sherry144260/hitcon-pcb-badge/fw/Core/Hitcon/App/tama_src/screens.h

#ifndef SCREENS_H
#define SCREENS_H

#include "simu_setting.h"
/// -- -- -- --

#define DISPLAY_WIDTH 16
#define DISPLAY_HEIGHT 8
#define COMMON_HEIGHT 8
#define IDLE_PET_WIDTH 8
#define SELECT_WIDTH 8
#define NUM_WIDTH 2
#define EGG_WIDTH 8
#define FOOD_HEART_OVERVIEW_ICON_WIDTH 4
#define FOOD_HEART_OVERVIEW_ICON_HEIGHT 4
#define WEAK_PET_WIDTH 8
#define WEAK_PET_PARTICLE_WIDTH 8
#define HOSPITAL_WIDTH 8
#define BATTLE_WIDTH 7
#define TRAINING_WIDTH 7
#define YN_WIDTH 16
#define YN_SELECT_LEFT_WIDTH 4
#define YN_SELECT_RIGHT_WIDTH 3

// m_xxx = material xxx

enum {
  FRAME_1,
  FRAME_2,
};

enum {
  PET_TYPE_DOG,
  PET_TYPE_CAT,
  OTHER_TYPE_TRAINING_FACILITY,
};

enum {
  BATTLE,
  TRAINING,
};

enum {
  LEFT,
  RIGHT,
};

enum {
  WIN,
  LOSE,
};

enum {
  PLAYER,
  ENEMY,
  NONE,
};

enum {
  cookie_100,
  cookie_50,
  cookie_30,
  cookie_0,
  ate_frame0,
  ate_frame1,
};

// the structure of compressed data
struct CompressedImage {
  uint8_t width;        // image width info
  uint8_t height;       // image height info
  const uint8_t* data;  // the pointer to the data
};

namespace hitcon {
namespace app {
namespace tama {
namespace components {

/**
 * @brief The compressed data of dog idle1.
 *
 * The original data is:
 *
 *  ```
 *  0, 0, 0, 0, 0, 0, 0, 0,  //
 *  0, 0, 0, 0, 0, 0, 0, 0,  //
 *  0, 0, 0, 0, 1, 0, 1, 0,  //
 *  1, 0, 0, 1, 1, 1, 1, 0,  //
 *  1, 0, 1, 1, 1, 1, 1, 1,  //
 *  1, 1, 1, 1, 1, 1, 1, 0,  //
 *  0, 1, 1, 1, 1, 1, 1, 0,  //
 *  0, 1, 0, 1, 0, 1, 0, 0,  //
 *  ```
 *
 * Notice: the compressed data is not directly mapping to the original data.
 * It packed the bits in a specific way.
 *
 */
constexpr uint8_t m_dog_idle1_compressed_data[] = {0x38, 0xE0, 0x70, 0xF8,
                                                   0x7C, 0xF8, 0x7C, 0x10};
constexpr CompressedImage m_dog_idle1_compressed = {
    .width = IDLE_PET_WIDTH,
    .height = COMMON_HEIGHT,
    .data = m_dog_idle1_compressed_data};

/**
 * @brief The compressed data of dog idle2.
 *
 * The original data is:
 *
 *  ```
 *  0, 0, 0, 0, 0, 0, 0, 0,  //
 *  0, 0, 0, 0, 0, 0, 0, 0,  //
 *  0, 0, 0, 0, 1, 0, 1, 0,  //
 *  0, 0, 0, 1, 1, 1, 1, 0,  //
 *  1, 0, 1, 1, 1, 1, 1, 1,  //
 *  1, 1, 1, 1, 1, 1, 1, 0,  //
 *  0, 1, 1, 1, 1, 1, 1, 0,  //
 *  0, 1, 0, 1, 0, 1, 0, 0,  //
 *  ```
 *
 * Notice: the compressed data is not directly mapping to the original data.
 * It packed the bits in a specific way.
 *
 */
constexpr uint8_t m_dog_idle2_compressed_data[] = {0x30, 0xE0, 0x70, 0xF8,
                                                   0x7C, 0xF8, 0x7C, 0x10};
constexpr CompressedImage m_dog_idle2_compressed = {
    .width = IDLE_PET_WIDTH,
    .height = COMMON_HEIGHT,
    .data = m_dog_idle2_compressed_data};

/**
 * @brief The compressed data of m_cat_idle1.
 *
 * The original data is:
 *
 *  ```
    0, 0, 0, 0, 0, 0, 0, 0,  //
    0, 0, 0, 0, 0, 0, 0, 0,  //
    0, 0, 0, 0, 0, 0, 0, 0,  //
    0, 0, 1, 0, 1, 0, 1, 0,  //
    0, 1, 0, 0, 1, 1, 1, 0,  //
    0, 1, 0, 1, 1, 1, 1, 0,  //
    0, 0, 1, 1, 1, 1, 1, 0,  //
    0, 0, 1, 0, 1, 0, 1, 0,  //
 *  ```
 *
 * Notice: the compressed data is not directly mapping to the original data.
 * It packed the bits in a specific way.
 *
 */
constexpr uint8_t m_cat_idle1_compressed_data[] = {0x00, 0x30, 0xC8, 0x60,
                                                   0xF8, 0x70, 0xF8, 0x00};
constexpr CompressedImage m_cat_idle1_compressed = {
    .width = IDLE_PET_WIDTH,
    .height = COMMON_HEIGHT,
    .data = m_cat_idle1_compressed_data};

/**
 * @brief The compressed data of m_cat_idle2.
 *
 * The original data is:
 *
 *  ```
 *  0, 0, 0, 0, 0, 0, 0, 0,  //
 *  0, 0, 0, 0, 0, 0, 0, 0,  //
 *  0, 0, 0, 0, 0, 0, 0, 0,  //
 *  1, 1, 0, 0, 1, 0, 1, 0,  //
 *  0, 0, 1, 0, 1, 1, 1, 0,  //
 *  0, 1, 0, 1, 1, 1, 1, 0,  //
 *  0, 0, 1, 1, 1, 1, 1, 0,  //
 *  0, 0, 1, 0, 1, 0, 1, 0,  //
 *  ```
 *
 * Notice: the compressed data is not directly mapping to the original data.
 * It packed the bits in a specific way.
 *
 */
constexpr uint8_t m_cat_idle2_compressed_data[] = {0x08, 0x28, 0xD0, 0x60,
                                                   0xF8, 0x70, 0xF8, 0x00};
constexpr CompressedImage m_cat_idle2_compressed = {
    .width = IDLE_PET_WIDTH,
    .height = COMMON_HEIGHT,
    .data = m_cat_idle2_compressed_data};

/**
 * @brief The compressed data of m_select_print_all_character.
 *
 * The original data is:
 *
 *  ```
 *  0, 0, 0, 0, 0, 0, 0, 0, 0, 0, 0, 0, 0, 0, 0, 0,  //
 *  0, 0, 0, 0, 0, 0, 0, 0, 0, 0, 0, 1, 0, 1, 0, 0,  //
 *  0, 0, 0, 0, 1, 0, 1, 0, 0, 0, 0, 1, 1, 1, 1, 0,  //
 *  0, 1, 0, 0, 1, 1, 1, 0, 1, 0, 1, 1, 1, 1, 1, 1,  //
 *  0, 1, 0, 1, 1, 1, 1, 0, 1, 1, 1, 1, 1, 1, 1, 0,  //
 *  0, 0, 1, 1, 1, 1, 1, 0, 0, 1, 1, 1, 1, 1, 1, 0,  //
 *  0, 0, 1, 0, 1, 0, 1, 0, 0, 1, 0, 1, 0, 1, 0, 0,  //
 *  0, 0, 0, 0, 0, 0, 0, 0, 0, 0, 0, 0, 0, 0, 0, 0,  //
 *  ```
 *
 * Notice: the compressed data is not directly mapping to the original data.
 * It packed the bits in a specific way.
 *
 */
constexpr uint8_t m_select_print_all_character_compressed_data[] = {
    0x00, 0x18, 0x60, 0x30, 0x7C, 0x38, 0x7C, 0x00,
    0x18, 0x70, 0x38, 0x7E, 0x3C, 0x7E, 0x3C, 0x08};
constexpr CompressedImage m_select_print_all_character_compressed = {
    .width = DISPLAY_WIDTH,
    .height = DISPLAY_HEIGHT,
    .data = m_select_print_all_character_compressed_data};

/**
 * @brief The compressed data of m_select_cursor.
 *
 * The original data is:
 *
 *  ```
 *  0, 1, 1, 1, 1, 1, 1, 0,  //
 *  1, 0, 0, 0, 0, 0, 0, 1,  //
 *  0, 0, 0, 0, 0, 0, 0, 0,  //
 *  0, 0, 0, 0, 0, 0, 0, 0,  //
 *  0, 0, 0, 0, 0, 0, 0, 0,  //
 *  0, 0, 0, 0, 0, 0, 0, 0,  //
 *  0, 0, 0, 0, 0, 0, 0, 0,  //
 *  1, 1, 1, 1, 1, 1, 1, 1,  //
 *  ```
 *
 * Notice: the compressed data is not directly mapping to the original data.
 * It packed the bits in a specific way.
 *
 */
constexpr uint8_t m_select_cursor_compressed_data[] = {0x82, 0x81, 0x81, 0x81,
                                                       0x81, 0x81, 0x81, 0x82};
constexpr CompressedImage m_select_cursor_compressed = {
    .width = SELECT_WIDTH,
    .height = COMMON_HEIGHT,
    .data = m_select_cursor_compressed_data};

/**
 * @brief The compressed data of m_dog_weak_compressed_data.
 *
 * The original data is:
 *
 *  ```
 *  0, 0, 0, 0, 0, 0, 0, 0,  //
 *  0, 0, 0, 0, 0, 0, 0, 0,  //
 *  0, 0, 0, 0, 0, 0, 0, 0,  //
 *  0, 0, 0, 0, 0, 0, 0, 0,  //
 *  0, 0, 0, 1, 0, 1, 0, 0,  //
 *  1, 1, 0, 1, 1, 1, 0, 0,  //
 *  0, 1, 1, 1, 1, 1, 1, 0,  //
 *  0, 1, 1, 1, 1, 1, 0, 0,  //
 *  ```
 *
 * Notice: the compressed data is not directly mapping to the original data.
 * It packed the bits in a specific way.
 */
constexpr uint8_t m_dog_weak_compressed_data[] = {0x20, 0xE0, 0xC0, 0xF0,
                                                  0xE0, 0xF0, 0x40, 0x00};
constexpr CompressedImage m_dog_weak_compressed = {
    .width = WEAK_PET_WIDTH,
    .height = COMMON_HEIGHT,
    .data = m_dog_weak_compressed_data};

/**
 * @brief The compressed data of m_cat_weak_compressed_data.
 *
 * The original data is:
 *
 *  ```
 *  0, 0, 0, 0, 0, 0, 0, 0,  //
 *  0, 0, 0, 0, 0, 0, 0, 0,  //
 *  0, 0, 0, 0, 0, 0, 0, 0,  //
 *  0, 0, 0, 0, 0, 0, 0, 0,  //
 *  1, 1, 0, 0, 1, 0, 1, 0,  //
 *  0, 0, 1, 0, 1, 1, 1, 0,  //
 *  0, 1, 0, 1, 1, 1, 1, 0,  //
 *  0, 0, 1, 1, 1, 1, 1, 0,  //
 *  ```
 *
 * Notice: the compressed data is not directly mapping to the original data.
 * It packed the bits in a specific way.
 *
 */
constexpr uint8_t m_cat_weak_compressed_data[] = {0x10, 0x50, 0xA0, 0xC0,
                                                  0xF0, 0xE0, 0xF0, 0x00};
constexpr CompressedImage m_cat_weak_compressed = {
    .width = WEAK_PET_WIDTH,
    .height = COMMON_HEIGHT,
    .data = m_cat_weak_compressed_data};

/**
 * @brief The compressed data of m_weak_particle_1_compressed_data.
 *
 * The original data is:
 *
 *  ```
 *  0, 0, 0, 0, 0, 0, 0, 0,  //
 *  0, 0, 0, 0, 1, 0, 0, 0,  //
 *  0, 0, 0, 0, 0, 0, 1, 0,  //
 *  0, 0, 1, 0, 0, 0, 0, 0,  //
 *  0, 0, 0, 0, 0, 0, 0, 0,  //
 *  0, 0, 0, 0, 0, 0, 0, 0,  //
 *  0, 0, 0, 0, 0, 0, 0, 0,  //
 *  0, 0, 0, 0, 0, 0, 0, 0,  //
 *  ```
 *
 * Notice: the compressed data is not directly mapping to the original data.
 * It packed the bits in a specific way.
 *
 */

constexpr uint8_t m_weak_particle_1_compressed_data[] = {
    0x00, 0x00, 0x08, 0x00, 0x02, 0x00, 0x04, 0x00};
constexpr CompressedImage m_weak_particle_1_compressed = {
    .width = WEAK_PET_PARTICLE_WIDTH,
    .height = COMMON_HEIGHT,
    .data = m_weak_particle_1_compressed_data};

/**
 * @brief The compressed data of m_weak_particle_2_compressed_data.
 *
 * The original data is:
 *
 *  ```
 *  0, 0, 0, 0, 0, 0, 0, 0,  //
 *  0, 0, 0, 0, 0, 0, 1, 0,  //
 *  0, 0, 1, 0, 1, 0, 0, 0,  //
 *  0, 0, 0, 0, 0, 0, 0, 0,  //
 *  0, 0, 0, 0, 0, 0, 0, 0,  //
 *  0, 0, 0, 0, 0, 0, 0, 0,  //
 *  0, 0, 0, 0, 0, 0, 0, 0,  //
 *  0, 0, 0, 0, 0, 0, 0, 0,  //
 *  ```
 *
 * Notice: the compressed data is not directly mapping to the original data.
 * It packed the bits in a specific way.
 *
 */

constexpr uint8_t m_weak_particle_2_compressed_data[] = {
    0x00, 0x00, 0x04, 0x00, 0x04, 0x00, 0x02, 0x00};
constexpr CompressedImage m_weak_particle_2_compressed = {
    .width = WEAK_PET_PARTICLE_WIDTH,
    .height = COMMON_HEIGHT,
    .data = m_weak_particle_2_compressed_data};

/**
 * @brief The compressed data of dog_battle_result.
 *
 * The original data is:
 *
 *  ```
 *  0, 0, 0, 0, 0, 0, 0,  //
 *  0, 0, 0, 0, 0, 0, 0,  //
 *  0, 0, 0, 0, 0, 0, 0,  //
 *  0, 0, 0, 0, 0, 0, 0,  //
 *  0, 0, 0, 1, 0, 1, 0,  //
 *  1, 1, 0, 1, 1, 1, 0,  //
 *  0, 1, 1, 1, 1, 1, 1,  //
 *  0, 1, 1, 1, 1, 1, 0,  //
 *  ```
 *
 * Notice: the compressed data is not directly mapping to the original data.
 * It packed the bits in a specific way.
 *
 */

constexpr uint8_t m_dog_battle_result_compressed_data[] = {
    0x20, 0xE0, 0xC0, 0xF0, 0xE0, 0xF0, 0x40};
constexpr CompressedImage m_dog_battle_result_compressed = {
    .width = 7, .height = 8, .data = m_dog_battle_result_compressed_data};

/**
 * @brief The compressed data of cat_battle_result.
 *
 * The original data is:
 *
 *  ```
 *  0, 0, 0, 0, 0, 0, 0,  //
 *  0, 0, 0, 0, 0, 0, 0,  //
 *  0, 0, 0, 0, 0, 0, 0,  //
 *  0, 0, 0, 0, 0, 0, 0,  //
 *  0, 0, 0, 0, 0, 0, 0,  //
 *  1, 1, 0, 0, 1, 0, 1,  //
 *  0, 0, 1, 0, 1, 1, 1,  //
 *  0, 1, 0, 1, 1, 1, 1,  //
 *  ```
 *
 * Notice: the compressed data is not directly mapping to the original data.
 * It packed the bits in a specific way.
 *
 */

constexpr uint8_t m_cat_battle_result_compressed_data[] = {
    0x20, 0xA0, 0x40, 0x80, 0xE0, 0xC0, 0xE0};
constexpr CompressedImage m_cat_battle_result_compressed = {
    .width = 7, .height = 8, .data = m_cat_battle_result_compressed_data};

/**
 * @brief The compressed data of battle_result_win_effect.
 *
 * The original data is:
 *
 *  ```
 *  0, 0, 0, 0, 1, 0, 0, 0, 1, 0, 0, 0, 1, 0, 0, 0,  //
 *  0, 1, 0, 0, 0, 1, 0, 0, 1, 0, 0, 1, 0, 0, 0, 1,  //
 *  0, 0, 1, 0, 0, 0, 1, 0, 0, 0, 1, 0, 0, 0, 1, 0,  //
 *  0, 0, 0, 1, 0, 0, 0, 0, 0, 0, 0, 0, 0, 1, 0, 0,  //
 *  0, 0, 0, 0, 0, 0, 0, 0, 0, 0, 0, 0, 0, 0, 0, 0,  //
 *  0, 0, 0, 0, 0, 0, 0, 0, 0, 0, 0, 0, 0, 0, 0, 0,  //
 *  0, 0, 0, 0, 0, 0, 0, 0, 0, 0, 0, 0, 0, 0, 0, 0,  //
 *  0, 0, 0, 0, 0, 0, 0, 0, 0, 0, 0, 0, 0, 0, 0, 0,  //
 *  ```
 *
 * Notice: the compressed data is not directly mapping to the original data.
 * It packed the bits in a specific way.
 *
 */

constexpr uint8_t m_battle_result_win_effect_compressed_data[] = {
    0x00, 0x02, 0x04, 0x08, 0x01, 0x02, 0x04, 0x00,
    0x03, 0x00, 0x04, 0x02, 0x01, 0x08, 0x04, 0x02};
constexpr CompressedImage m_battle_result_win_effect_compressed = {
    .width = 16,
    .height = 8,
    .data = m_battle_result_win_effect_compressed_data};

/**
 * @brief The compressed data of battle_result_lost_effect.
 *
 * The original data is:
 *
 *  ```
 *  0, 0, 0, 0, 0, 0, 0, 0, 0, 0, 0, 0, 0, 0, 0, 0,  //
 *  0, 0, 0, 0, 0, 0, 0, 0, 0, 0, 0, 0, 0, 0, 0, 0,  //
 *  0, 0, 1, 0, 1, 0, 1, 0, 1, 0, 1, 0, 1, 0, 0, 0,  //
 *  0, 0, 0, 0, 0, 0, 0, 0, 0, 0, 0, 0, 0, 0, 0, 0,  //
 *  0, 0, 0, 0, 0, 0, 0, 0, 0, 0, 0, 0, 0, 0, 0, 0,  //
 *  0, 0, 0, 0, 0, 0, 0, 0, 0, 0, 0, 0, 0, 0, 0, 0,  //
 *  0, 0, 0, 0, 0, 0, 0, 0, 0, 0, 0, 0, 0, 0, 0, 0,  //
 *  0, 0, 0, 0, 0, 0, 0, 0, 0, 0, 0, 0, 0, 0, 0, 0,  //
 *  ```
 *
 * Notice: the compressed data is not directly mapping to the original data.
 * It packed the bits in a specific way.
 *
 */

constexpr uint8_t m_battle_result_lose_effect_compressed_data[] = {
    0x00, 0x00, 0x04, 0x00, 0x04, 0x00, 0x04, 0x00,
    0x04, 0x00, 0x04, 0x00, 0x04, 0x00, 0x00, 0x00};
constexpr CompressedImage m_battle_result_lose_effect_compressed = {
    .width = 16,
    .height = 8,
    .data = m_battle_result_lose_effect_compressed_data};

/**
 * @brief The compressed data of m_player_dog.
 *
 * The original data same as m_dog_battle_result_compressed.
 *
 */
constexpr CompressedImage m_player_dog_compressed =
    m_dog_battle_result_compressed;

/**
 * @brief The compressed data of m_player_cat.
 *
 * The original data is:
 *
 *  ```
 *  0, 0, 0, 0, 0, 0, 0,  //
 *  0, 0, 0, 0, 0, 0, 0,  //
 *  0, 0, 0, 0, 0, 0, 0,  //
 *  0, 0, 0, 0, 0, 0, 0,  //
 *  1, 1, 0, 0, 1, 0, 1,  //
 *  0, 0, 1, 0, 1, 1, 1,  //
 *  0, 1, 0, 1, 1, 1, 1,  //
 *  0, 0, 1, 1, 1, 1, 1,  //
 *  ```
 *
 * Notice: the compressed data is not directly mapping to the original data.
 * It packed the bits in a specific way.
 *
 */

constexpr uint8_t m_player_cat_compressed_data[] = {0x10, 0x50, 0xA0, 0xC0,
                                                    0xF0, 0xE0, 0xF0};
constexpr CompressedImage m_player_cat_compressed = {
    .width = 7, .height = 8, .data = m_player_cat_compressed_data};

/**
 * @brief The compressed data of m_enemy_dog.
 *
 * The original data is:
 *
 *  ```
 *  0, 1, 0, 1, 0, 0, 0,  //
 *  0, 1, 1, 1, 0, 0, 1,  //
 *  1, 1, 1, 1, 1, 1, 1,  //
 *  0, 1, 1, 1, 1, 1, 0,  //
 *  0, 1, 0, 1, 0, 1, 0,  //
 *  0, 0, 0, 0, 0, 0, 0,  //
 *  0, 0, 0, 0, 0, 0, 0,  //
 *  0, 0, 0, 0, 0, 0, 0,  //
 *  ```
 *
 * Notice: the compressed data is not directly mapping to the original data.
 * It packed the bits in a specific way.
 *
 */

constexpr uint8_t m_enemy_dog_compressed_data[] = {0x04, 0x1F, 0x0E, 0x1F,
                                                   0x0C, 0x1C, 0x06};
constexpr CompressedImage m_enemy_dog_compressed = {
    .width = 7, .height = 8, .data = m_enemy_dog_compressed_data};

/**
 * @brief The compressed data of m_enemy_cat.
 *
 * The original data is:
 *
 *  ```
 *  0, 0, 0, 0, 0, 0, 0,  //
 *  1, 0, 1, 0, 0, 1, 1,  //
 *  1, 1, 1, 0, 1, 0, 0,  //
 *  1, 1, 1, 1, 0, 1, 0,  //
 *  1, 1, 1, 1, 1, 0, 0,  //
 *  1, 0, 1, 0, 1, 0, 0,  //
 *  0, 0, 0, 0, 0, 0, 0,  //
 *  0, 0, 0, 0, 0, 0, 0,  //
 *  ```
 *
 * Notice: the compressed data is not directly mapping to the original data.
 * It packed the bits in a specific way.
 *
 */

constexpr uint8_t m_enemy_cat_compressed_data[] = {0x3E, 0x1C, 0x3E, 0x18,
                                                   0x34, 0x0A, 0x02};
constexpr CompressedImage m_enemy_cat_compressed = {
    .width = 7, .height = 8, .data = m_enemy_cat_compressed_data};

/**
 * @brief The compressed data of m_training_facility_enemy.
 *
 * The original data is:
 *
 *  ```
 *  0, 0, 1, 0, 0, 0, 0,  //
 *  0, 1, 0, 1, 0, 1, 0,  //
 *  0, 1, 0, 1, 1, 0, 1,  //
 *  0, 0, 1, 0, 1, 0, 1,  //
 *  0, 0, 1, 0, 0, 1, 0,  //
 *  0, 1, 1, 1, 0, 1, 0,  //
 *  0, 0, 0, 0, 1, 1, 1,  //
 *  0, 0, 0, 0, 0, 0, 0,  //
 *  ```
 *
 * Notice: the compressed data is not directly mapping to the original data.
 * It packed the bits in a specific way.
 *
 */

constexpr uint8_t m_training_facility_enemy_compressed_data[] = {
    0x00, 0x26, 0x39, 0x26, 0x4C, 0x72, 0x4C};
constexpr CompressedImage m_training_facility_enemy_compressed = {
    .width = 7, .height = 8, .data = m_training_facility_enemy_compressed_data};

/**
 * @brief The compressed data of m_hit_player_effect.
 *
 * The original data is:
 *
 *  ```
 *  0, 0, 0, 0, 0, 0, 0, 0,  //
 *  0, 0, 0, 0, 0, 0, 0, 0,  //
 *  0, 0, 0, 0, 0, 0, 0, 0,  //
 *  1, 0, 0, 1, 0, 0, 0, 0,  //
 *  0, 1, 0, 0, 1, 0, 0, 0,  //
 *  0, 0, 1, 0, 0, 1, 0, 0,  //
 *  0, 0, 0, 1, 0, 0, 1, 0,  //
 *  0, 0, 0, 0, 1, 0, 0, 1,  //
 *  ```
 *
 * Notice: the compressed data is not directly mapping to the original data.
 * It packed the bits in a specific way.
 *
 */

constexpr uint8_t m_hit_player_effect_compressed_data[] = {
    0x08, 0x10, 0x20, 0x48, 0x90, 0x20, 0x40, 0x80};
constexpr CompressedImage m_hit_player_effect_compressed = {
    .width = 8, .height = 8, .data = m_hit_player_effect_compressed_data};

/**
 * @brief The compressed data of m_hit_enemy_effect.
 *
 * The original data is:
 *
 *  ```
 *  1, 0, 0, 1, 0, 0, 0, 0,  //
 *  0, 1, 0, 0, 1, 0, 0, 0,  //
 *  0, 0, 1, 0, 0, 1, 0, 0,  //
 *  0, 0, 0, 1, 0, 0, 1, 0,  //
 *  0, 0, 0, 0, 1, 0, 0, 1,  //
 *  0, 0, 0, 0, 0, 0, 0, 0,  //
 *  0, 0, 0, 0, 0, 0, 0, 0,  //
 *  0, 0, 0, 0, 0, 0, 0, 0,  //
 *  ```
 *
 * Notice: the compressed data is not directly mapping to the original data.
 * It packed the bits in a specific way.
 *
 */

constexpr uint8_t m_hit_enemy_effect_compressed_data[] = {
    0x01, 0x02, 0x04, 0x09, 0x12, 0x04, 0x08, 0x10};
constexpr CompressedImage m_hit_enemy_effect_compressed = {
    .width = 8, .height = 8, .data = m_hit_enemy_effect_compressed_data};

}  // namespace components

namespace egg_icon {

/**
 * @brief The compressed data of m_egg_75_percent_up.
 *
 * The original data is:
 *
 *  ```
 *  0, 0, 0, 0, 0, 0, 0, 0,  //
 *  0, 0, 0, 0, 0, 0, 0, 0,  //
 *  0, 0, 0, 1, 1, 0, 0, 0,  //
 *  0, 0, 1, 1, 1, 1, 0, 0,  //
 *  0, 1, 1, 1, 1, 1, 1, 0,  //
 *  0, 1, 1, 1, 1, 1, 1, 0,  //
 *  0, 1, 1, 1, 1, 1, 1, 0,  //
 *  0, 0, 1, 1, 1, 1, 0, 0,  //
 *  ```
 *
 * Notice: the compressed data is not directly mapping to the original data.
 * It packed the bits in a specific way.
 *
 */
constexpr uint8_t m_egg_75_percent_up_compressed_data[] = {
    0x00, 0x70, 0xF8, 0xFC, 0xFC, 0xF8, 0x70, 0x00};
constexpr CompressedImage m_egg_75_percent_up_compressed = {
    .width = EGG_WIDTH,
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
 *
 */
constexpr uint8_t m_egg_hatch_shinning1_compressed_data[] = {
    0x10, 0x54, 0x00, 0xC6, 0x00, 0x54, 0x10, 0x00};
constexpr CompressedImage m_egg_hatch_shinning1_compressed = {
    .width = EGG_WIDTH,
    .height = COMMON_HEIGHT,
    .data = m_egg_hatch_shinning1_compressed_data};

/**
 * @brief The compressed data of m_egg_hatch_shinning2.
 *
 * The original data is:
 *
 *  ```
 *  0, 0, 0, 0, 0, 0, 0, 0,  //
 *  0, 0, 0, 0, 0, 0, 0, 0,  //
 *  0, 0, 0, 1, 0, 0, 0, 0,  //
 *  0, 0, 1, 0, 1, 0, 0, 0,  //
 *  0, 1, 0, 0, 0, 1, 0, 0,  //
 *  0, 0, 1, 0, 1, 0, 0, 0,  //
 *  0, 0, 0, 1, 0, 0, 0, 0,  //
 *  0, 0, 0, 0, 0, 0, 0, 0,  //
 *  ```
 *
 * Notice: the compressed data is not directly mapping to the original data.
 * It packed the bits in a specific way.
 *
 */
constexpr uint8_t m_egg_hatch_shinning2_compressed_data[] = {
    0x00, 0x10, 0x28, 0x44, 0x28, 0x10, 0x00, 0x00};
constexpr CompressedImage m_egg_hatch_shinning2_compressed = {
    .width = EGG_WIDTH,
    .height = COMMON_HEIGHT,
    .data = m_egg_hatch_shinning2_compressed_data};
}  // namespace egg_icon

namespace menu_icon {

/**
 * @brief The compressed data of m_icon_zero.
 *
 * The original data is:
 *
 *  ```
 *  0, 0,  //
 *  0, 0,  //
 *  0, 0,  //
 *  1, 1,  //
 *  1, 1,  //
 *  1, 1,  //
 *  1, 1,  //
 *  1, 1,  //
 *  ```
 *
 * Notice: the compressed data is not directly mapping to the original data.
 * It packed the bits in a specific way.
 *
 */
constexpr uint8_t m_icon_zero_compressed_data[] = {0xF8, 0xF8};
constexpr CompressedImage m_icon_zero_compressed = {
    .width = NUM_WIDTH,
    .height = COMMON_HEIGHT,
    .data = m_icon_zero_compressed_data};

/**
 * @brief The compressed data of m_icon_one.
 *
 * The original data is:
 *
 *  ```
 *  0, 0,  //
 *  0, 0,  //
 *  0, 0,  //
 *  0, 1,  //
 *  0, 1,  //
 *  0, 1,  //
 *  0, 1,  //
 *  0, 1,  //
 *  ```
 *
 * Notice: the compressed data is not directly mapping to the original data.
 * It packed the bits in a specific way.
 *
 */
constexpr uint8_t m_icon_one_compressed_data[] = {0x00, 0xF8};
constexpr CompressedImage m_icon_one_compressed = {
    .width = NUM_WIDTH,
    .height = COMMON_HEIGHT,
    .data = m_icon_one_compressed_data};

/**
 * @brief The compressed data of m_icon_two.
 *
 * The original data is:
 *
 *  ```
 *  0, 0,  //
 *  0, 0,  //
 *  0, 0,  //
 *  1, 1,  //
 *  0, 1,  //
 *  1, 1,  //
 *  1, 0,  //
 *  1, 1,  //
 *  ```
 *
 * Notice: the compressed data is not directly mapping to the original data.
 * It packed the bits in a specific way.
 *
 */
constexpr uint8_t m_icon_two_compressed_data[] = {0xE8, 0xB8};
constexpr CompressedImage m_icon_two_compressed = {
    .width = NUM_WIDTH,
    .height = COMMON_HEIGHT,
    .data = m_icon_two_compressed_data};

/**
 * @brief The compressed data of m_icon_three.
 *
 * The original data is:
 *
 *  ```
 *  0, 0,  //
 *  0, 0,  //
 *  0, 0,  //
 *  1, 1,  //
 *  0, 1,  //
 *  1, 1,  //
 *  0, 1,  //
 *  1, 1,  //
 *  ```
 *
 * Notice: the compressed data is not directly mapping to the original data.
 * It packed the bits in a specific way.
 *
 */
constexpr uint8_t m_icon_three_compressed_data[] = {0xA8, 0xF8};
constexpr CompressedImage m_icon_three_compressed = {
    .width = NUM_WIDTH,
    .height = COMMON_HEIGHT,
    .data = m_icon_three_compressed_data};

/**
 * @brief The compressed data of m_icon_four.
 *
 * The original data is:
 *
 *  ```
 *  0, 0,  //
 *  0, 0,  //
 *  0, 0,  //
 *  1, 0,  //
 *  1, 0,  //
 *  1, 1,  //
 *  0, 1,  //
 *  0, 1,  //
 *  ```
 *
 * Notice: the compressed data is not directly mapping to the original data.
 * It packed the bits in a specific way.
 *
 */
constexpr uint8_t m_icon_four_compressed_data[] = {0x38, 0xE0};
constexpr CompressedImage m_icon_four_compressed = {
    .width = NUM_WIDTH,
    .height = COMMON_HEIGHT,
    .data = m_icon_four_compressed_data};

/**
 * @brief The compressed data of m_icon_five.
 *
 * The original data is:
 *
 *  ```
 *  0, 0,  //
 *  0, 0,  //
 *  0, 0,  //
 *  1, 1,  //
 *  1, 0,  //
 *  1, 1,  //
 *  0, 1,  //
 *  1, 1,  //
 *  ```
 *
 * Notice: the compressed data is not directly mapping to the original data.
 * It packed the bits in a specific way.
 *
 */
constexpr uint8_t m_icon_five_compressed_data[] = {0xB8, 0xE8};
constexpr CompressedImage m_icon_five_compressed = {
    .width = NUM_WIDTH,
    .height = COMMON_HEIGHT,
    .data = m_icon_five_compressed_data};

/**
 * @brief The compressed data of m_icon_six.
 *
 * The original data is:
 *
 *  ```
 *  0, 0,  //
 *  0, 0,  //
 *  0, 0,  //
 *  1, 1,  //
 *  1, 0,  //
 *  1, 1,  //
 *  1, 1,  //
 *  1, 1,  //
 *  ```
 *
 * Notice: the compressed data is not directly mapping to the original data.
 * It packed the bits in a specific way.
 *
 */
constexpr uint8_t m_icon_six_compressed_data[] = {0xF8, 0xE8};
constexpr CompressedImage m_icon_six_compressed = {
    .width = NUM_WIDTH,
    .height = COMMON_HEIGHT,
    .data = m_icon_six_compressed_data};

/**
 * @brief The compressed data of m_icon_seven.
 *
 * The original data is:
 *
 *  ```
 *  0, 0,  //
 *  0, 0,  //
 *  0, 0,  //
 *  1, 1,  //
 *  0, 1,  //
 *  0, 1,  //
 *  0, 1,  //
 *  0, 1,  //
 *  ```
 *
 * Notice: the compressed data is not directly mapping to the original data.
 * It packed the bits in a specific way.
 *
 */
constexpr uint8_t m_icon_seven_compressed_data[] = {0x08, 0xF8};
constexpr CompressedImage m_icon_seven_compressed = {
    .width = NUM_WIDTH,
    .height = COMMON_HEIGHT,
    .data = m_icon_seven_compressed_data};

/**
 * @brief The compressed data of m_icon_eight.
 *
 * The original data is:
 *
 *  ```
 *  0, 0,  //
 *  0, 0,  //
 *  0, 0,  //
 *  1, 1,  //
 *  1, 1,  //
 *  0, 0,  //
 *  1, 1,  //
 *  1, 1,  //
 *  ```
 *
 * Notice: the compressed data is not directly mapping to the original data.
 * It packed the bits in a specific way.
 *
 */
constexpr uint8_t m_icon_eight_compressed_data[] = {0xD8, 0xD8};
constexpr CompressedImage m_icon_eight_compressed = {
    .width = NUM_WIDTH,
    .height = COMMON_HEIGHT,
    .data = m_icon_eight_compressed_data};

/**
 * @brief The compressed data of m_icon_nine.
 *
 * The original data is:
 *
 *  ```
 *  0, 0,  //
 *  0, 0,  //
 *  0, 0,  //
 *  1, 1,  //
 *  1, 1,  //
 *  1, 1,  //
 *  0, 1,  //
 *  1, 1,  //
 *  ```
 *
 * Notice: the compressed data is not directly mapping to the original data.
 * It packed the bits in a specific way.
 *
 */
constexpr uint8_t m_icon_nine_compressed_data[] = {0xB8, 0xF8};
constexpr CompressedImage m_icon_nine_compressed = {
    .width = NUM_WIDTH,
    .height = COMMON_HEIGHT,
    .data = m_icon_nine_compressed_data};

constexpr CompressedImage m_num_icon_compressed[10] = {
    m_icon_zero_compressed,  m_icon_one_compressed,   m_icon_two_compressed,
    m_icon_three_compressed, m_icon_four_compressed,  m_icon_five_compressed,
    m_icon_six_compressed,   m_icon_seven_compressed, m_icon_eight_compressed,
    m_icon_nine_compressed};

/**
 * @brief The compressed data of m_icon_important.
 *
 * The original data is:
 *
 *  ```
 *  0, 0,  //
 *  0, 0,  //
 *  0, 0,  //
 *  0, 1,  //
 *  0, 1,  //
 *  0, 1,  //
 *  0, 0,  //
 *  0, 1,  //
 *  ```
 *
 * Notice: the compressed data is not directly mapping to the original data.
 * It packed the bits in a specific way.
 *
 */
constexpr uint8_t m_icon_important_compressed_data[] = {0x00, 0xB8};
constexpr CompressedImage m_icon_important_compressed = {
    .width = NUM_WIDTH,
    .height = COMMON_HEIGHT,
    .data = m_icon_important_compressed_data};

/**
 * @brief The compressed data of m_icon_status_overview_heart.
 *
 * The original data is:
 *
 *  ```
 *  0, 0, 0, 0,  //
 *  0, 1, 0, 1,  //
 *  0, 1, 1, 1,  //
 *  0, 0, 1, 0,  //
 *  ```
 *
 * Notice: the compressed data is not directly mapping to the original data.
 * It packed the bits in a specific way.
 *
 */
constexpr uint8_t m_icon_status_overview_heart_compressed_data[] = {0x00, 0x06,
                                                                    0x0C, 0x06};
constexpr CompressedImage m_icon_status_overview_heart_compressed = {
    .width = FOOD_HEART_OVERVIEW_ICON_WIDTH,
    .height = FOOD_HEART_OVERVIEW_ICON_HEIGHT,
    .data = m_icon_status_overview_heart_compressed_data};

/**
 * @brief The compressed data of m_icon_status_overview_food.
 *
 * The original data is:
 *
 *  ```
 *  0, 0, 0, 0,  //
 *  0, 0, 1, 0,  //
 *  0, 1, 0, 1,  //
 *  0, 0, 1, 0,  //
 *  ```
 *
 * Notice: the compressed data is not directly mapping to the original data.
 * It packed the bits in a specific way.
 *
 */
constexpr uint8_t m_icon_status_overview_food_compressed_data[] = {0x00, 0x04,
                                                                   0x0A, 0x04};
constexpr CompressedImage m_icon_status_overview_food_compressed = {
    .width = FOOD_HEART_OVERVIEW_ICON_WIDTH,
    .height = FOOD_HEART_OVERVIEW_ICON_HEIGHT,
    .data = m_icon_status_overview_food_compressed_data};

/**
 * @brief The compressed data of m_icon_hospital_compressed_data.
 *
 * The original data is:
 *
 *  ```
 *  0, 0, 0, 0, 0, 0, 0, 0,  //
 *  0, 0, 0, 1, 1, 0, 0, 0,  //
 *  0, 0, 0, 1, 1, 0, 0, 0,  //
 *  0, 1, 1, 1, 1, 1, 1, 0,  //
 *  0, 1, 1, 1, 1, 1, 1, 0,  //
 *  0, 0, 0, 1, 1, 0, 0, 0,  //
 *  0, 0, 0, 1, 1, 0, 0, 0,  //
 *  0, 0, 0, 0, 0, 0, 0, 0,  //
 *  ```
 *
 * Notice: the compressed data is not directly mapping to the original data.
 * It packed the bits in a specific way.
 *
 */

constexpr uint8_t m_icon_hospital_compressed_data[] = {0x00, 0x18, 0x18, 0x7E,
                                                       0x7E, 0x18, 0x18, 0x00};
constexpr CompressedImage m_icon_hospital_compressed = {
    .width = HOSPITAL_WIDTH,
    .height = COMMON_HEIGHT,
    .data = m_icon_hospital_compressed_data};

/**
 * @brief The compressed data of m_battle_icon.
 *
 * The original data is:
 *
 *  ```
 *  0, 0, 0, 0, 0, 0, 0,  //
 *  0, 0, 0, 0, 0, 1, 1,  //
 *  0, 0, 0, 0, 1, 0, 1,  //
 *  0, 1, 0, 1, 0, 1, 0,  //
 *  0, 1, 1, 0, 1, 0, 0,  //
 *  0, 0, 1, 1, 0, 0, 0,  //
 *  0, 1, 0, 1, 1, 0, 0,  //
 *  1, 0, 0, 0, 0, 0, 0,  //
 *  ```
 *
 * Notice: the compressed data is not directly mapping to the original data.
 * It packed the bits in a specific way.
 *
 */

constexpr uint8_t m_battle_icon_compressed_data[] = {0x80, 0x58, 0x30, 0x68,
                                                     0x54, 0x0A, 0x06};
constexpr CompressedImage m_battle_icon_compressed = {
    .width = BATTLE_WIDTH,
    .height = COMMON_HEIGHT,
    .data = m_battle_icon_compressed_data};

/**
 * @brief The compressed data of m_training_icon.
 *
 * The original data is:
 *
 *  ```
 *  0, 0, 0, 0, 0, 0, 0,  //
 *  0, 1, 0, 0, 0, 1, 0,  //
 *  1, 1, 0, 0, 0, 1, 1,  //
 *  1, 1, 1, 1, 1, 1, 1,  //
 *  1, 1, 0, 0, 0, 1, 1,  //
 *  0, 1, 0, 0, 0, 1, 0,  //
 *  0, 0, 0, 0, 0, 0, 0,  //
 *  0, 0, 0, 0, 0, 0, 0,  //
 *  ```
 *
 * Notice: the compressed data is not directly mapping to the original data.
 * It packed the bits in a specific way.
 *
 */

constexpr uint8_t m_training_icon_compressed_data[] = {0x1C, 0x3E, 0x08, 0x08,
                                                       0x08, 0x3E, 0x1C};
constexpr CompressedImage m_training_icon_compressed = {
    .width = TRAINING_WIDTH,
    .height = COMMON_HEIGHT,
    .data = m_training_icon_compressed_data};

/**
 * @brief The compressed data of m_YN_icon.
 *
 * The original data is:
 *
 *  ```
 *  0, 0, 0, 0, 0, 0, 0, 0, 0, 0, 0, 0, 0, 0, //
 *  0, 0, 0, 0, 0, 0, 0, 0, 0, 0, 0, 0, 0, 0, //
 *  1, 0, 0, 1, 0, 0, 0, 0, 0, 0, 0, 1, 0, 1, //
 *  1, 1, 0, 1, 0, 0, 0, 0, 0, 0, 0, 1, 0, 1, //
 *  1, 0, 1, 1, 0, 0, 0, 0, 0, 0, 0, 1, 1, 1, //
 *  1, 0, 0, 1, 0, 0, 0, 0, 0, 0, 0, 0, 1, 0, //
 *  0, 0, 0, 0, 0, 0, 0, 0, 0, 0, 0, 0, 0, 0, //
 *  0, 0, 0, 0, 0, 0, 0, 0, 0, 0, 0, 0, 0, 0, //
 *  ```
 *
 * Notice: the compressed data is not directly mapping to the original data.
 * It packed the bits in a specific way.
 *
 */

constexpr uint8_t m_YN_icon_compressed_data[] = {
    0x3C, 0x08, 0x10, 0x3C, 0x00, 0x00, 0x00, 0x00,
    0x00, 0x00, 0x00, 0x00, 0x00, 0x1C, 0x30, 0x1C};
constexpr CompressedImage m_YN_icon_compressed = {
    .width = YN_WIDTH,
    .height = COMMON_HEIGHT,
    .data = m_YN_icon_compressed_data};

/**
 * @brief The compressed data of m_YN_select_cursor_left.
 *
 * The original data is:
 *
 *  ```
 *  0, 0, 0, 0,  //
 *  0, 0, 0, 0,  //
 *  0, 0, 0, 0,  //
 *  0, 0, 0, 0,  //
 *  0, 0, 0, 0,  //
 *  0, 0, 0, 0,  //
 *  0, 0, 0, 0,  //
 *  1, 1, 1, 1,  //
 *  ```
 *
 * Notice: the compressed data is not directly mapping to the original data.
 * It packed the bits in a specific way.
 *
 */

constexpr uint8_t m_YN_select_cursor_left_compressed_data[] = {0x80, 0x80, 0x80,
                                                               0x80};
constexpr CompressedImage m_YN_select_cursor_left_compressed = {
    .width = YN_SELECT_LEFT_WIDTH,
    .height = COMMON_HEIGHT,
    .data = m_YN_select_cursor_left_compressed_data};

/**
 * @brief The compressed data of m_YN_select_cursor_right.
 *
 * The original data is:
 *
 *  ```
 *  0, 0, 0,  //
 *  0, 0, 0,  //
 *  0, 0, 0,  //
 *  0, 0, 0,  //
 *  0, 0, 0,  //
 *  0, 0, 0,  //
 *  0, 0, 0,  //
 *  1, 1, 1,  //
 *  ```
 *
 * Notice: the compressed data is not directly mapping to the original data.
 * It packed the bits in a specific way.
 *
 */

constexpr uint8_t m_YN_select_cursor_right_compressed_data[] = {0x80, 0x80,
                                                                0x80};
constexpr CompressedImage m_YN_select_cursor_right_compressed = {
    .width = YN_SELECT_RIGHT_WIDTH,
    .height = COMMON_HEIGHT,
    .data = m_YN_select_cursor_right_compressed_data};

/**
 * @brief The compressed data of m_lv_word_icon (level).
 *
 * The original data is:
 *
 *  ```
 *  0, 0, 0, 0, 0, 0, 0,  //
 *  1, 1, 1, 1, 1, 1, 1,  //
 *  0, 0, 0, 0, 0, 0, 0,  //
 *  1, 0, 0, 0, 1, 0, 1,  //
 *  1, 0, 0, 0, 1, 0, 1,  //
 *  1, 0, 0, 0, 1, 0, 1,  //
 *  1, 0, 0, 0, 1, 0, 1,  //
 *  1, 1, 1, 0, 0, 1, 0,  //
 *  ```
 *
 * Notice: the compressed data is not directly mapping to the original data.
 * It packed the bits in a specific way.
 *
 */

constexpr uint8_t m_lv_word_icon_compressed_data[] = {0xFA, 0x82, 0x82, 0x02,
                                                      0x7A, 0x82, 0x7A};
constexpr CompressedImage m_lv_word_icon_compressed = {
    .width = 7,
    .height = COMMON_HEIGHT,
    .data = m_lv_word_icon_compressed_data};

/**
 * @brief The compressed data of m_fd_word_icon (food).
 *
 * The original data is:
 *
 *  ```
 *  0, 0, 0, 0, 0, 0, 0,  //
 *  1, 1, 1, 1, 1, 1, 1,  //
 *  0, 0, 0, 0, 0, 0, 0,  //
 *  1, 1, 1, 0, 1, 1, 0,  //
 *  1, 0, 0, 0, 1, 0, 1,  //
 *  1, 1, 1, 0, 1, 0, 1,  //
 *  1, 0, 0, 0, 1, 0, 1,  //
 *  1, 0, 0, 0, 1, 1, 0,  //
 *  ```
 *
 * Notice: the compressed data is not directly mapping to the original data.
 * It packed the bits in a specific way.
 *
 */

constexpr uint8_t m_fd_word_icon_compressed_data[] = {0xFA, 0x2A, 0x2A, 0x02,
                                                      0xFA, 0x8A, 0x72};
constexpr CompressedImage m_fd_word_icon_compressed = {
    .width = 7,
    .height = COMMON_HEIGHT,
    .data = m_fd_word_icon_compressed_data};

/**
 * @brief The compressed data of m_hp_word_icon (health point).
 *
 * The original data is:
 *
 *  ```
 *  0, 0, 0, 0, 0, 0, 0,  //
 *  1, 1, 1, 1, 1, 1, 1,  //
 *  0, 0, 0, 0, 0, 0, 0,  //
 *  1, 0, 1, 0, 1, 1, 1,  //
 *  1, 0, 1, 0, 1, 0, 1,  //
 *  1, 1, 1, 0, 1, 1, 1,  //
 *  1, 0, 1, 0, 1, 0, 0,  //
 *  1, 0, 1, 0, 1, 0, 0,  //
 *  ```
 *
 * Notice: the compressed data is not directly mapping to the original data.
 * It packed the bits in a specific way.
 *
 */

constexpr uint8_t m_hp_word_icon_compressed_data[] = {0xFA, 0x22, 0xFA, 0x02,
                                                      0xFA, 0x2A, 0x3A};
constexpr CompressedImage m_hp_word_icon_compressed = {
    .width = 7,
    .height = COMMON_HEIGHT,
    .data = m_hp_word_icon_compressed_data};

/**
 * @brief The compressed data of m_heart_icon_detail.
 *
 * The original data is:
 *
 *  ```
 *  1, 0, 1,  //
 *  1, 1, 1,  //
 *  0, 1, 0,  //
 *  ```
 *
 * Notice: the compressed data is not directly mapping to the original data.
 * It packed the bits in a specific way.
 *
 */

constexpr uint8_t m_heart_icon_detail_compressed_data[] = {0x03, 0x06, 0x03};
constexpr CompressedImage m_heart_icon_detail_compressed = {
    .width = 3, .height = 3, .data = m_heart_icon_detail_compressed_data};

/**
 * @brief The compressed data of m_food_icon_detail.
 *
 * The original data is:
 *
 *  ```
 *  0, 1, 0,  //
 *  1, 0, 1,  //
 *  1, 1, 1,  //
 *  ```
 *
 * Notice: the compressed data is not directly mapping to the original data.
 * It packed the bits in a specific way.
 *
 */

constexpr uint8_t m_food_icon_detail_compressed_data[] = {0x06, 0x05, 0x06};
constexpr CompressedImage m_food_icon_detail_compressed = {
    .width = 3, .height = 3, .data = m_food_icon_detail_compressed_data};

/**
 * @brief The compressed data of m_cookie_100_icon.
 *
 * The original data is:
 *
 *  ```
 *  0, 0, 0, 0, 0, 0, 0,  //
 *  0, 0, 1, 1, 1, 0, 0,  //
 *  0, 1, 1, 1, 0, 1, 0,  //
 *  1, 1, 0, 1, 1, 1, 1,  //
 *  1, 1, 1, 1, 1, 0, 1,  //
 *  1, 0, 1, 1, 1, 1, 1,  //
 *  0, 1, 1, 0, 1, 1, 0,  //
 *  0, 0, 1, 1, 1, 0, 0,  //
 *  ```
 *
 * Notice: the compressed data is not directly mapping to the original data.
 * It packed the bits in a specific way.
 *
 */

constexpr uint8_t m_cookie_100_icon_compressed_data[] = {0x38, 0x5C, 0xF6, 0xBE,
                                                         0xFA, 0x6C, 0x38};
constexpr CompressedImage m_cookie_100_icon_compressed = {
    .width = 7, .height = 8, .data = m_cookie_100_icon_compressed_data};

/**
 * @brief The compressed data of m_cookie_50_icon.
 *
 * The original data is:
 *
 *  ```
 * 0, 0, 0, 0, 0, 0, 0,  //
 * 0, 0, 0, 1, 0, 0, 0,  //
 * 0, 1, 0, 0, 0, 0, 0,  //
 * 1, 0, 0, 1, 0, 1, 0,  //
 * 1, 1, 1, 0, 1, 0, 1,  //
 * 1, 0, 1, 1, 1, 1, 1,  //
 * 0, 1, 1, 0, 1, 1, 0,  //
 * 0, 0, 1, 1, 1, 0, 0,  //
 *  ```
 *
 * Notice: the compressed data is not directly mapping to the original data.
 * It packed the bits in a specific way.
 *
 */

constexpr uint8_t m_cookie_50_icon_compressed_data[] = {0x38, 0x54, 0xF0, 0xAA,
                                                        0xF0, 0x68, 0x30};
constexpr CompressedImage m_cookie_50_icon_compressed = {
    .width = 7, .height = 8, .data = m_cookie_50_icon_compressed_data};

/**
 * @brief The compressed data of m_cookie_30_icon.
 *
 * The original data is:
 *
 *  ```
 * 0, 0, 0, 0, 0, 0, 0,  //
 * 0, 0, 0, 0, 0, 0, 0,  //
 * 0, 0, 0, 0, 0, 0, 0,  //
 * 0, 0, 0, 1, 0, 0, 0,  //
 * 0, 1, 0, 0, 0, 1, 0,  //
 * 1, 0, 1, 0, 0, 0, 0,  //
 * 0, 1, 0, 1, 0, 1, 0,  //
 * 0, 0, 1, 0, 1, 0, 0,  //
 *  ```
 *
 * Notice: the compressed data is not directly mapping to the original data.
 * It packed the bits in a specific way.
 *
 */

constexpr uint8_t m_cookie_30_icon_compressed_data[] = {0x20, 0x50, 0xA0, 0x48,
                                                        0x80, 0x50, 0x00};
constexpr CompressedImage m_cookie_30_icon_compressed = {
    .width = 7, .height = 8, .data = m_cookie_30_icon_compressed_data};

/**
 * @brief The compressed data of m_cookie_0_icon.
 *
 * The original data is:
 *
 *  ```
 * 0, 0, 0, 0, 0, 0, 0, 0, 0, 0, 0, 0, 0, 0, 0, 0, //
 * 0, 0, 0, 0, 0, 0, 0, 0, 0, 0, 0, 0, 0, 0, 0, 0, //
 * 0, 0, 0, 0, 0, 0, 0, 0, 0, 0, 0, 0, 0, 0, 0, 0, //
 * 0, 0, 0, 0, 0, 0, 0, 0, 0, 0, 0, 0, 0, 0, 0, 0, //
 * 0, 0, 0, 0, 0, 0, 0, 0, 0, 0, 0, 0, 0, 0, 0, 0, //
 * 0, 0, 0, 0, 0, 0, 0, 0, 0, 0, 0, 0, 0, 0, 0, 0, //
 * 0, 0, 0, 0, 0, 0, 0, 0, 0, 0, 0, 0, 0, 0, 0, 0, //
 * 0, 0, 0, 0, 0, 0, 0, 0, 0, 0, 0, 0, 0, 0, 0, 0, //
 *  ```
 *
 * Notice: the compressed data is not directly mapping to the original data.
 * It packed the bits in a specific way.
 *
 */

constexpr uint8_t m_empty_frame_compressed_data[] = {
    0x00, 0x00, 0x00, 0x00, 0x00, 0x00, 0x00, 0x00,
    0x00, 0x00, 0x00, 0x00, 0x00, 0x00, 0x00, 0x00,
};
constexpr CompressedImage m_empty_frame_compressed = {
    .width = 16, .height = 8, .data = m_empty_frame_compressed_data};

/**
 * @brief The compressed data of m_battle_training_end.
 *
 * The original data is:
 *
 *  ```
 *  0, 0, 0, 0, 0, 0, 0, 0, 0, 0, 0, 0, 0, 0, 0, 0,  //
 *  0, 0, 0, 0, 0, 0, 0, 0, 0, 0, 0, 0, 0, 0, 0, 0,  //
 *  0, 0, 1, 1, 1, 0, 1, 0, 0, 1, 0, 1, 1, 1, 0, 0,  //
 *  0, 0, 1, 0, 0, 0, 1, 1, 0, 1, 0, 1, 0, 0, 1, 0,  //
 *  0, 0, 1, 1, 1, 0, 1, 1, 1, 1, 0, 1, 0, 0, 1, 0,  //
 *  0, 0, 1, 0, 0, 0, 1, 0, 1, 1, 0, 1, 0, 0, 1, 0,  //
 *  0, 0, 1, 1, 1, 0, 1, 0, 0, 1, 0, 1, 1, 1, 0, 0,  //
 *  0, 0, 0, 0, 0, 0, 0, 0, 0, 0, 0, 0, 0, 0, 0, 0,  //
 *  ```
 *
 * Notice: the compressed data is not directly mapping to the original data.
 * It packed the bits in a specific way.
 *
 */

constexpr uint8_t m_battle_training_end_compressed_data[] = {
    0x00, 0x00, 0x7C, 0x54, 0x54, 0x00, 0x7C, 0x18,
    0x30, 0x7C, 0x00, 0x7C, 0x44, 0x44, 0x38, 0x00};
constexpr CompressedImage m_battle_training_end_compressed = {
    .width = 16, .height = 8, .data = m_battle_training_end_compressed_data};

/**
 * @brief The compressed data of m_scoring_page_icon.
 *
 * The original data is:
 *
 *  ```
 *  0, 0, 0, 0, 0,  //
 *  0, 1, 0, 1, 0,  //
 *  0, 1, 0, 1, 0,  //
 *  0, 0, 1, 0, 0,  //
 *  0, 0, 0, 0, 0,  //
 *  0, 1, 0, 1, 0,  //
 *  0, 0, 1, 0, 0,  //
 *  0, 1, 0, 1, 0,  //
 *  ```
 *
 * Notice: the compressed data is not directly mapping to the original data.
 * It packed the bits in a specific way.
 *
 */

constexpr uint8_t m_scoring_page_icon_compressed_data[] = {0x00, 0xA6, 0x48,
                                                           0xA6, 0x00};
constexpr CompressedImage m_scoring_page_icon_compressed = {
    .width = 5, .height = 8, .data = m_scoring_page_icon_compressed_data};

/**
 * @brief The compressed data of m_score_icon.
 *
 * The original data is:
 *
 *  ```
 *  1, //
 *  1, //
 *  1, //
 *  ```
 *
 * Notice: the compressed data is not directly mapping to the original data.
 * It packed the bits in a specific way.
 *
 */

constexpr uint8_t m_score_icon_compressed_data[] = {
    0x07,
};
constexpr CompressedImage m_score_icon_compressed = {
    .width = 1, .height = 3, .data = m_score_icon_compressed_data};

}  // namespace menu_icon

}  // namespace tama
}  // namespace app
}  // namespace hitcon

#ifdef SIMU
constexpr uint8_t m_example_of_compress[] = {
    1, 1, 1, 1, 1, 1, 1, 1,  //
    0, 1, 1, 1, 1, 1, 1, 1,  //
    0, 0, 1, 1, 1, 1, 1, 1,  //
    0, 0, 0, 1, 1, 1, 1, 1,  //
    0, 0, 0, 0, 1, 1, 1, 1,  //
    0, 0, 0, 0, 0, 1, 1, 1,  //
    0, 0, 0, 0, 0, 0, 1, 1,  //
    0, 0, 0, 0, 0, 0, 0, 1,  //
};
#endif

/*---------- */

// template
/**
 * @brief The compressed data of .
 *
 * The original data is:
 *
 *  ```
 *
 *  ```
 *
 * Notice: the compressed data is not directly mapping to the original data.
 * It packed the bits in a specific way.
 *
 */

// constexpr uint8_t _compressed_data[] = {};
// constexpr CompressedImage _compressed = {
//     .width =, .height =, .data = _compressed_data};

#endif
