sherry144260/hitcon-pcb-badge/fw/Core/Src/tim.c

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
/* Includes ------------------------------------------------------------------*/
#include "tim.h"

TIM_HandleTypeDef htim1;
TIM_HandleTypeDef htim2;
TIM_HandleTypeDef htim3;
TIM_HandleTypeDef htim4;
DMA_HandleTypeDef hdma_tim1_up;
DMA_HandleTypeDef hdma_tim2_ch3;
DMA_HandleTypeDef hdma_tim3_ch3;
DMA_HandleTypeDef hdma_tim4_ch2;

/* TIM1 init function */
void MX_TIM1_Init(void)
{

  TIM_ClockConfigTypeDef sClockSourceConfig = {0};
  TIM_MasterConfigTypeDef sMasterConfig = {0};

  htim1.Instance = TIM1;
  htim1.Init.Prescaler = 5-1;
  htim1.Init.CounterMode = TIM_COUNTERMODE_UP;
  htim1.Init.Period = 1500-1;
  htim1.Init.ClockDivision = TIM_CLOCKDIVISION_DIV1;
  htim1.Init.RepetitionCounter = 0;
  htim1.Init.AutoReloadPreload = TIM_AUTORELOAD_PRELOAD_ENABLE;
  if (HAL_TIM_Base_Init(&htim1) != HAL_OK)
  {
    Error_Handler();
  }
  sClockSourceConfig.ClockSource = TIM_CLOCKSOURCE_INTERNAL;
  if (HAL_TIM_ConfigClockSource(&htim1, &sClockSourceConfig) != HAL_OK)
  {
    Error_Handler();
  }
  sMasterConfig.MasterOutputTrigger = TIM_TRGO_UPDATE;
  sMasterConfig.MasterSlaveMode = TIM_MASTERSLAVEMODE_DISABLE;
  if (HAL_TIMEx_MasterConfigSynchronization(&htim1, &sMasterConfig) != HAL_OK)
  {
    Error_Handler();
  }
}
/* TIM2 init function */
void MX_TIM2_Init(void)
{

  TIM_SlaveConfigTypeDef sSlaveConfig = {0};
  TIM_MasterConfigTypeDef sMasterConfig = {0};
  TIM_OC_InitTypeDef sConfigOC = {0};

  htim2.Instance = TIM2;
  htim2.Init.Prescaler = 0;
  htim2.Init.CounterMode = TIM_COUNTERMODE_UP;
  htim2.Init.Period = 4-1;
  htim2.Init.ClockDivision = TIM_CLOCKDIVISION_DIV1;
  htim2.Init.AutoReloadPreload = TIM_AUTORELOAD_PRELOAD_DISABLE;
  if (HAL_TIM_Base_Init(&htim2) != HAL_OK)
  {
    Error_Handler();
  }
  if (HAL_TIM_PWM_Init(&htim2) != HAL_OK)
  {
    Error_Handler();
  }
  sSlaveConfig.SlaveMode = TIM_SLAVEMODE_EXTERNAL1;
  sSlaveConfig.InputTrigger = TIM_TS_ITR2;
  if (HAL_TIM_SlaveConfigSynchro(&htim2, &sSlaveConfig) != HAL_OK)
  {
    Error_Handler();
  }
  sMasterConfig.MasterOutputTrigger = TIM_TRGO_UPDATE;
  sMasterConfig.MasterSlaveMode = TIM_MASTERSLAVEMODE_DISABLE;
  if (HAL_TIMEx_MasterConfigSynchronization(&htim2, &sMasterConfig) != HAL_OK)
  {
    Error_Handler();
  }
  sConfigOC.OCMode = TIM_OCMODE_PWM1;
  sConfigOC.Pulse = 2;
  sConfigOC.OCPolarity = TIM_OCPOLARITY_HIGH;
  sConfigOC.OCFastMode = TIM_OCFAST_DISABLE;
  if (HAL_TIM_PWM_ConfigChannel(&htim2, &sConfigOC, TIM_CHANNEL_3) != HAL_OK)
  {
    Error_Handler();
  }
}
/* TIM3 init function */
void MX_TIM3_Init(void)
{

  TIM_ClockConfigTypeDef sClockSourceConfig = {0};
  TIM_MasterConfigTypeDef sMasterConfig = {0};
  TIM_OC_InitTypeDef sConfigOC = {0};

  htim3.Instance = TIM3;
  htim3.Init.Prescaler = 5-1;
  htim3.Init.CounterMode = TIM_COUNTERMODE_UP;
  htim3.Init.Period = 63-1;
  htim3.Init.ClockDivision = TIM_CLOCKDIVISION_DIV1;
  htim3.Init.AutoReloadPreload = TIM_AUTORELOAD_PRELOAD_DISABLE;
  if (HAL_TIM_Base_Init(&htim3) != HAL_OK)
  {
    Error_Handler();
  }
  sClockSourceConfig.ClockSource = TIM_CLOCKSOURCE_INTERNAL;
  if (HAL_TIM_ConfigClockSource(&htim3, &sClockSourceConfig) != HAL_OK)
  {
    Error_Handler();
  }
  if (HAL_TIM_PWM_Init(&htim3) != HAL_OK)
  {
    Error_Handler();
  }
  sMasterConfig.MasterOutputTrigger = TIM_TRGO_UPDATE;
  sMasterConfig.MasterSlaveMode = TIM_MASTERSLAVEMODE_ENABLE;
  if (HAL_TIMEx_MasterConfigSynchronization(&htim3, &sMasterConfig) != HAL_OK)
  {
    Error_Handler();
  }
  sConfigOC.OCMode = TIM_OCMODE_PWM1;
  sConfigOC.Pulse = 16;
  sConfigOC.OCPolarity = TIM_OCPOLARITY_HIGH;
  sConfigOC.OCFastMode = TIM_OCFAST_DISABLE;
  if (HAL_TIM_PWM_ConfigChannel(&htim3, &sConfigOC, TIM_CHANNEL_3) != HAL_OK)
  {
    Error_Handler();
  }
  /* USER CODE BEGIN TIM3_Init 2 */
#ifdef V1_1
  sConfigOC.OCMode = TIM_OCMODE_PWM2;
  sConfigOC.Pulse = 30;
  if (HAL_TIM_PWM_ConfigChannel(&htim3, &sConfigOC, TIM_CHANNEL_2) != HAL_OK) {
    Error_Handler();
  }
#elifdef V2_1
sConfigOC.OCMode = TIM_OCMODE_PWM2;
  sConfigOC.Pulse = 30;
  if (HAL_TIM_PWM_ConfigChannel(&htim3, &sConfigOC, TIM_CHANNEL_1) != HAL_OK) {
    Error_Handler();
  }
#endif
  /* USER CODE END TIM3_Init 2 */
  HAL_TIM_MspPostInit(&htim3);

}
/* TIM4 init function */
void MX_TIM4_Init(void)
{

  TIM_ClockConfigTypeDef sClockSourceConfig = {0};
  TIM_MasterConfigTypeDef sMasterConfig = {0};
  TIM_OC_InitTypeDef sConfigOC = {0};

  htim4.Instance = TIM4;
  htim4.Init.Prescaler = 12000-1;
  htim4.Init.CounterMode = TIM_COUNTERMODE_UP;
  htim4.Init.Period = 10-1;
  htim4.Init.ClockDivision = TIM_CLOCKDIVISION_DIV1;
  htim4.Init.AutoReloadPreload = TIM_AUTORELOAD_PRELOAD_DISABLE;
  if (HAL_TIM_Base_Init(&htim4) != HAL_OK)
  {
    Error_Handler();
  }
  sClockSourceConfig.ClockSource = TIM_CLOCKSOURCE_INTERNAL;
  if (HAL_TIM_ConfigClockSource(&htim4, &sClockSourceConfig) != HAL_OK)
  {
    Error_Handler();
  }
  if (HAL_TIM_PWM_Init(&htim4) != HAL_OK)
  {
    Error_Handler();
  }
  sMasterConfig.MasterOutputTrigger = TIM_TRGO_RESET;
  sMasterConfig.MasterSlaveMode = TIM_MASTERSLAVEMODE_DISABLE;
  if (HAL_TIMEx_MasterConfigSynchronization(&htim4, &sMasterConfig) != HAL_OK)
  {
    Error_Handler();
  }
  sConfigOC.OCMode = TIM_OCMODE_PWM1;
  sConfigOC.Pulse = 5;
  sConfigOC.OCPolarity = TIM_OCPOLARITY_HIGH;
  sConfigOC.OCFastMode = TIM_OCFAST_DISABLE;
  if (HAL_TIM_PWM_ConfigChannel(&htim4, &sConfigOC, TIM_CHANNEL_2) != HAL_OK)
  {
    Error_Handler();
  }
}

void HAL_TIM_Base_MspInit(TIM_HandleTypeDef* tim_baseHandle)
{

  if(tim_baseHandle->Instance==TIM1)
  {
    /* TIM1 clock enable */
    __HAL_RCC_TIM1_CLK_ENABLE();

    /* TIM1 DMA Init */
    /* TIM1_UP Init */
    hdma_tim1_up.Instance = DMA1_Channel5;
    hdma_tim1_up.Init.Direction = DMA_MEMORY_TO_PERIPH;
    hdma_tim1_up.Init.PeriphInc = DMA_PINC_DISABLE;
    hdma_tim1_up.Init.MemInc = DMA_MINC_ENABLE;
    hdma_tim1_up.Init.PeriphDataAlignment = DMA_PDATAALIGN_WORD;
    hdma_tim1_up.Init.MemDataAlignment = DMA_MDATAALIGN_WORD;
    hdma_tim1_up.Init.Mode = DMA_CIRCULAR;
    hdma_tim1_up.Init.Priority = DMA_PRIORITY_LOW;
    if (HAL_DMA_Init(&hdma_tim1_up) != HAL_OK)
    {
      Error_Handler();
    }

    __HAL_LINKDMA(tim_baseHandle,hdma[TIM_DMA_ID_UPDATE],hdma_tim1_up);

  }
  else if(tim_baseHandle->Instance==TIM2)
  {
    /* TIM2 clock enable */
    __HAL_RCC_TIM2_CLK_ENABLE();

    /* TIM2 DMA Init */
    /* TIM2_CH3 Init */
    hdma_tim2_ch3.Instance = DMA1_Channel1;
    hdma_tim2_ch3.Init.Direction = DMA_PERIPH_TO_MEMORY;
    hdma_tim2_ch3.Init.PeriphInc = DMA_PINC_DISABLE;
    hdma_tim2_ch3.Init.MemInc = DMA_MINC_ENABLE;
    hdma_tim2_ch3.Init.PeriphDataAlignment = DMA_PDATAALIGN_HALFWORD;
    hdma_tim2_ch3.Init.MemDataAlignment = DMA_MDATAALIGN_HALFWORD;
    hdma_tim2_ch3.Init.Mode = DMA_CIRCULAR;
    hdma_tim2_ch3.Init.Priority = DMA_PRIORITY_LOW;
    if (HAL_DMA_Init(&hdma_tim2_ch3) != HAL_OK)
    {
      Error_Handler();
    }

    __HAL_LINKDMA(tim_baseHandle,hdma[TIM_DMA_ID_CC3],hdma_tim2_ch3);

  }
  else if(tim_baseHandle->Instance==TIM3)
  {
    /* TIM3 clock enable */
    __HAL_RCC_TIM3_CLK_ENABLE();

    /* TIM3 DMA Init */
    /* TIM3_CH3 Init */
    hdma_tim3_ch3.Instance = DMA1_Channel2;
    hdma_tim3_ch3.Init.Direction = DMA_MEMORY_TO_PERIPH;
    hdma_tim3_ch3.Init.PeriphInc = DMA_PINC_DISABLE;
    hdma_tim3_ch3.Init.MemInc = DMA_MINC_ENABLE;
    hdma_tim3_ch3.Init.PeriphDataAlignment = DMA_PDATAALIGN_HALFWORD;
    hdma_tim3_ch3.Init.MemDataAlignment = DMA_MDATAALIGN_HALFWORD;
    hdma_tim3_ch3.Init.Mode = DMA_CIRCULAR;
    hdma_tim3_ch3.Init.Priority = DMA_PRIORITY_LOW;
    if (HAL_DMA_Init(&hdma_tim3_ch3) != HAL_OK)
    {
      Error_Handler();
    }

    __HAL_LINKDMA(tim_baseHandle,hdma[TIM_DMA_ID_CC3],hdma_tim3_ch3);

  }
  else if(tim_baseHandle->Instance==TIM4)
  {
    /* TIM4 clock enable */
    __HAL_RCC_TIM4_CLK_ENABLE();

    /* TIM4 DMA Init */
    /* TIM4_CH2 Init */
    hdma_tim4_ch2.Instance = DMA1_Channel4;
    hdma_tim4_ch2.Init.Direction = DMA_PERIPH_TO_MEMORY;
    hdma_tim4_ch2.Init.PeriphInc = DMA_PINC_DISABLE;
    hdma_tim4_ch2.Init.MemInc = DMA_MINC_ENABLE;
    hdma_tim4_ch2.Init.PeriphDataAlignment = DMA_PDATAALIGN_HALFWORD;
    hdma_tim4_ch2.Init.MemDataAlignment = DMA_MDATAALIGN_HALFWORD;
    hdma_tim4_ch2.Init.Mode = DMA_NORMAL;
    hdma_tim4_ch2.Init.Priority = DMA_PRIORITY_LOW;
    if (HAL_DMA_Init(&hdma_tim4_ch2) != HAL_OK)
    {
      Error_Handler();
    }

    __HAL_LINKDMA(tim_baseHandle,hdma[TIM_DMA_ID_CC2],hdma_tim4_ch2);

  }
}
void HAL_TIM_MspPostInit(TIM_HandleTypeDef* timHandle)
{

  GPIO_InitTypeDef GPIO_InitStruct = {0};
  if(timHandle->Instance==TIM3)
  {
    __HAL_RCC_GPIOB_CLK_ENABLE();
    /**TIM3 GPIO Configuration
    PB0     ------> TIM3_CH3
    */
    GPIO_InitStruct.Pin = IrTx_Pin;
    GPIO_InitStruct.Mode = GPIO_MODE_AF_PP;
    GPIO_InitStruct.Speed = GPIO_SPEED_FREQ_LOW;
    HAL_GPIO_Init(IrTx_GPIO_Port, &GPIO_InitStruct);

  /* USER CODE BEGIN TIM3_MspPostInit 1 */

#ifdef V1_1
    // PB5     ------> TIM3_CH2
    GPIO_InitStruct.Pin = DEC_EN_Pin;
    GPIO_InitStruct.Mode = GPIO_MODE_AF_PP;
    GPIO_InitStruct.Speed = GPIO_SPEED_FREQ_LOW;
    HAL_GPIO_Init(DEC_EN_GPIO_Port, &GPIO_InitStruct);

    __HAL_AFIO_REMAP_TIM3_PARTIAL();
#elifdef V2_1
    // PB4     ------> TIM3_CH1
    GPIO_InitStruct.Pin = DEC_EN_Pin;
    GPIO_InitStruct.Mode = GPIO_MODE_AF_PP;
    GPIO_InitStruct.Speed = GPIO_SPEED_FREQ_LOW;
    HAL_GPIO_Init(DEC_EN_GPIO_Port, &GPIO_InitStruct);

    __HAL_AFIO_REMAP_TIM3_PARTIAL();

#endif
  /* USER CODE END TIM3_MspPostInit 1 */
  }

}

void HAL_TIM_Base_MspDeInit(TIM_HandleTypeDef* tim_baseHandle)
{

  if(tim_baseHandle->Instance==TIM1)
  {
    /* Peripheral clock disable */
    __HAL_RCC_TIM1_CLK_DISABLE();

    /* TIM1 DMA DeInit */
    HAL_DMA_DeInit(tim_baseHandle->hdma[TIM_DMA_ID_UPDATE]);
  }
  else if(tim_baseHandle->Instance==TIM2)
  {
    /* Peripheral clock disable */
    __HAL_RCC_TIM2_CLK_DISABLE();

    /* TIM2 DMA DeInit */
    HAL_DMA_DeInit(tim_baseHandle->hdma[TIM_DMA_ID_CC3]);
  }
  else if(tim_baseHandle->Instance==TIM3)
  {
    /* Peripheral clock disable */
    __HAL_RCC_TIM3_CLK_DISABLE();

    /* TIM3 DMA DeInit */
    HAL_DMA_DeInit(tim_baseHandle->hdma[TIM_DMA_ID_CC3]);
  }
  else if(tim_baseHandle->Instance==TIM4)
  {
    /* Peripheral clock disable */
    __HAL_RCC_TIM4_CLK_DISABLE();

    /* TIM4 DMA DeInit */
    HAL_DMA_DeInit(tim_baseHandle->hdma[TIM_DMA_ID_CC2]);
  }
}
