sherry144260/hitcon-pcb-badge/fw/Core/Hitcon/Service/ImuService.cc

#include <Service/ImuService.h>

#include "stm32f1xx_hal_i2c.h"

using namespace hitcon;

namespace {
void I2CCallbackWrapper(I2C_HandleTypeDef* hi2c) {
  if (hi2c == I2C_HANDLE) g_imu_service.I2CCallback();
}
}  // namespace

namespace hitcon {

ImuService g_imu_service;

ImuService::ImuService()
    : _routine_task(417, (task_callback_t)&ImuService::Routine, this, 100),
      state(State::INIT), _rx_cb(nullptr), _rx_cb_arg1(nullptr),
      _is_rx_called(true), _tx_cb(nullptr), _tx_cb_arg1(nullptr),
      _is_tx_called(true) {}

void ImuService::Init() {
  HAL_I2C_RegisterCallback(&hi2c1, HAL_I2C_MEM_RX_COMPLETE_CB_ID,
                           I2CCallbackWrapper);
  HAL_I2C_RegisterCallback(&hi2c1, HAL_I2C_MEM_TX_COMPLETE_CB_ID,
                           I2CCallbackWrapper);
  HAL_I2C_RegisterCallback(&hi2c1, HAL_I2C_MASTER_RX_COMPLETE_CB_ID,
                           I2CCallbackWrapper);
  HAL_I2C_RegisterCallback(&hi2c1, HAL_I2C_MASTER_TX_COMPLETE_CB_ID,
                           I2CCallbackWrapper);
  state = State::IDLE;
  scheduler.Queue(&_routine_task, nullptr);
  scheduler.EnablePeriodic(&_routine_task);
}

void ImuService::QueueReadReg(uint8_t addr, uint8_t* value) {
  if (_rx_queue.IsFull()) my_assert(false);

  ReadOp op = {addr, value};
  _rx_queue.PushFront(op);
  _is_rx_called = false;
}

void ImuService::QueueWriteReg(uint8_t addr, uint8_t value) {
  if (_tx_queue.IsFull()) my_assert(false);

  WriteOp op = {addr, value};
  _tx_queue.PushFront(op);
  _is_tx_called = false;
}

void ImuService::SetRxCallback(callback_t callback, void* callback_arg1) {
  _rx_cb = callback;
  _rx_cb_arg1 = callback_arg1;
}

void ImuService::SetTxCallback(callback_t callback, void* callback_arg1) {
  _tx_cb = callback;
  _tx_cb_arg1 = callback_arg1;
}

void ImuService::I2CCallback() {
  if (state == State::READING) {
    _rx_queue.PopBack();

    if (_rx_queue.IsEmpty() && _rx_cb != nullptr && !_is_rx_called) {
      _rx_cb(_rx_cb_arg1, nullptr);
      _is_rx_called = true;
    }
  } else if (state == State::WRITING) {
    _tx_queue.PopBack();

    if (_tx_queue.IsEmpty() && _tx_cb != nullptr && !_is_tx_called) {
      _tx_cb(_tx_cb_arg1, nullptr);
      _is_tx_called = true;
    }
  }

  state = State::IDLE;
}

void ImuService::Routine(void* arg) {
  if (state != State::IDLE) return;

  HAL_StatusTypeDef status = HAL_OK;
  if (!_tx_queue.IsEmpty()) {
    WriteOp& op = _tx_queue.Back();
    state = State::WRITING;

    status = HAL_I2C_Mem_Write_IT(I2C_HANDLE, SLAVE_ADDR, op.addr,
                                  I2C_MEMADD_SIZE_8BIT, &op.value, 1);
  } else if (!_rx_queue.IsEmpty()) {
    ReadOp& op = _rx_queue.Back();
    state = State::READING;

    status = HAL_I2C_Mem_Read_IT(I2C_HANDLE, SLAVE_ADDR, op.addr,
                                 I2C_MEMADD_SIZE_8BIT, op.value_ptr, 1);
  }
  if (status != HAL_OK) {
    state = State::IDLE;
    my_assert(false);
  }
}

}  // namespace hitcon
