sherry144260/hitcon-pcb-badge/fw/Core/Hitcon/Service/EcParams.h

#ifndef SERVICE_EC_PARAMS_H_
#define SERVICE_EC_PARAMS_H_

#include <stddef.h>

namespace hitcon {

constexpr size_t ECC_SIGNATURE_SIZE = 14;
constexpr size_t ECC_PUBKEY_SIZE = 8;

}  // namespace hitcon

#endif  // SERVICE_EC_PARAMS_H_
