sherry144260/hitcon-pcb-badge/fw/Core/Hitcon/App/HardwareTestApp.h

#ifndef HARDWARE_TEST_APP
#define HARDWARE_TEST_APP

#include <Logic/IrController.h>
#include <Service/Sched/PeriodicTask.h>

#include "app.h"

using namespace hitcon::service::sched;
namespace hitcon {
enum TEST_APP_STATE {  // TODO: add xboard connect/disconnect test
  TS_DISPLAY_SET_ALL = 1,
  TS_DISPLAY_RESET_ALL,
  TS_DISPLAY_CHECKER,
  TS_DISPLAY_BRIGHTNESS,
  TS_BTN_BRIGHTNESS,
  TS_BTN_BACK,
  TS_BTN_UP,
  TS_BTN_MODE,
  TS_BTN_LEFT,
  TS_BTN_OK,
  TS_BTN_RIGHT,
  TS_BTN_DOWN,
  TS_XBOARD,
  TS_IR,
  TS_GYRO,
  TS_ACC,
  TS_PASS = 50,
  TS_FAIL = 99,
};

constexpr int PERIOD = 1000;

class HardwareTestApp : public App {
 public:
  HardwareTestApp();
  virtual ~HardwareTestApp() = default;

  void OnEntry() override;
  void OnExit() override;
  void OnButton(button_t button) override;
  void Init();
  void CheckIr(void* arg1);

  PeriodicTask task;
  static constexpr size_t IR_TEST_LEN = 9;

 private:
  uint32_t current_state;
  uint32_t next_state;
  uint32_t start_tick;
  uint8_t _count;
  hitcon::ir::IrData _ir_data;
  uint8_t _ir_data_len;
  void Routine(void* unused);
  void CheckXBoard(void* arg1);
  void CheckImu(void* arg1);
};

extern HardwareTestApp hardware_test_app;

}  // namespace hitcon

#endif  // HARDWARE_TEST_APP
