sherry144260/hitcon-pcb-badge/fw/Core/Hitcon/App/tama_src/screen_simu.cpp

// #define SIMU  // open if needed
#define TEST_ALL_FRAMES

#ifdef SIMU
#define SLEEP_US 500000

#include "TamaAppFrame.h"

/*--- simulation relative start---*/
/**
 * @brief The function to show the full screen in terminal. Will only use in
 * simulation.
 *
 * @param buf the frame to be displayed
 */
void display_input(const uint8_t* buf) {
  std::cout << "┌";
  for (int x = 0; x < DISPLAY_WIDTH; ++x) std::cout << "──";
  std::cout << "┐\n";

  for (int y = 0; y < DISPLAY_HEIGHT; ++y) {
    std::cout << "│";
    for (int x = 0; x < DISPLAY_WIDTH; ++x) {
      uint8_t pixel = buf[y * DISPLAY_WIDTH + x];
      std::cout << (pixel ? "██" : "  ");
      // std::cout << (pixel ? "1" : "0");
    }
    std::cout << "│\n";
  }

  std::cout << "└";
  for (int x = 0; x < DISPLAY_WIDTH; ++x) std::cout << "──";
  std::cout << "┘\n";
}

/**
 * @brief Show frame change in terminal.
 *
 * @param frame_collection A array contain frames
 * @param frame_count The len of frame_collection
 * @param delay_us How long to sleep between frames
 */
void show_anime_with_delay(const uint8_t** frame_collection, int frame_count,
                           int delay_us) {
  for (int i = 0; i < frame_count; ++i) {
    // display_input
    display_input(*(frame_collection + i));
    // delay
    usleep(delay_us);
  }
}
/*--- simulation relative end--- */

/* ------ example part ----- */
// Just examples of how to use

/**
 * @brief The example of cat_idle
 *
 * @param repeat_count How many times should frame_collection repeat
 */
void cat_idle(int repeat_count) {
  component_info cat_idle_component_info = {
      .x_len = 8,
      .y_len = 8,
      .x_offset = 0,
      .y_offset = 0,
  };
  base_info screen_info = {
      .width = 16,
      .height = 8,
  };
  const CompressedImage* target = &m_cat_idle1_compressed;
  uint8_t decompressed_buffer[target->width * target->height];
  decompress_component(target, decompressed_buffer);
  uint8_t cat_idle1[screen_info.width * screen_info.height];
  stack_component(decompressed_buffer, cat_idle1, cat_idle_component_info,
                  screen_info);

  const CompressedImage* target2 = &m_cat_idle2_compressed;
  uint8_t decompressed_buffer2[target2->width * target2->height];
  decompress_component(target2, decompressed_buffer2);
  uint8_t cat_idle2[screen_info.width * screen_info.height];
  stack_component(decompressed_buffer, cat_idle2, cat_idle_component_info,
                  screen_info);
  const uint8_t* cat_idle_frame_all[CAT_IDLE_FRAME_COUNT] = {cat_idle1,
                                                             cat_idle2};
  for (int i = 0; i < repeat_count; ++i) {
    show_anime_with_delay(cat_idle_frame_all, CAT_IDLE_FRAME_COUNT, SLEEP_US);
  }
}

/**
 * @brief The example of dog_idle
 *
 * @param repeat_count How many times should frame_collection repeat
 */
void dog_idle(int repeat_count) {
  component_info dog_idle_component_info = {
      .x_len = 8,
      .y_len = 8,
      .x_offset = 0,
      .y_offset = 0,
  };
  base_info screen_info = {
      .width = 16,
      .height = 8,
  };

  const CompressedImage* target = &m_dog_idle1_compressed;
  uint8_t decompressed_buffer[target->width * target->height];
  decompress_component(target, decompressed_buffer);
  uint8_t dog_idle1[screen_info.width * screen_info.height];
  stack_component(decompressed_buffer, dog_idle1, dog_idle_component_info,
                  screen_info);

  const CompressedImage* target2 = &m_dog_idle2_compressed;
  uint8_t decompressed_buffer2[target2->width * target2->height];
  decompress_component(target2, decompressed_buffer2);
  uint8_t dog_idle2[screen_info.width * screen_info.height];
  stack_component(decompressed_buffer, dog_idle2, dog_idle_component_info,
                  screen_info);
  const uint8_t* dog_idle_frame_all[DOG_IDLE_FRAME_COUNT] = {dog_idle1,
                                                             dog_idle2};
  for (int i = 0; i < repeat_count; ++i) {
    show_anime_with_delay(dog_idle_frame_all, DOG_IDLE_FRAME_COUNT, SLEEP_US);
  }
}

/**
 * @brief The example of select_character
 *
 * @param repeat_count How many times should frame_collection repeat
 */
void select_character(int repeat_count) {
  uint8_t select_left[DISPLAY_WIDTH * DISPLAY_HEIGHT] = {0};
  uint8_t select_right[DISPLAY_WIDTH * DISPLAY_HEIGHT] = {0};
  get_select_character_frame(LEFT, select_left);
  get_select_character_frame(RIGHT, select_right);

  const uint8_t* select_character_frame_all[SELECT_CHARACTER_FRAME_COUNT] = {
      select_left, select_right};

  // show animation
  for (int i = 0; i < repeat_count; ++i) {
    show_anime_with_delay(select_character_frame_all,
                          SELECT_CHARACTER_FRAME_COUNT, SLEEP_US);
  }
}

/**
 * @brief The example of egg hatch
 *
 * The example counts down from 390 to 0, and shows the different hatching
 * scene.
 *
 * @param repeat_count How many times should frame_collection repeat
 */
void egg_hatch(int repeat_count) {
  // demo case:
  // (remaining_count)
  // 390 > 290 > 190 > 90 > (shine1, shine2)x repeat_shine_count

  uint8_t frame1[DISPLAY_WIDTH * DISPLAY_HEIGHT] = {0};
  uint8_t frame2[DISPLAY_WIDTH * DISPLAY_HEIGHT] = {0};
  uint8_t frame3[DISPLAY_WIDTH * DISPLAY_HEIGHT] = {0};
  uint8_t frame4[DISPLAY_WIDTH * DISPLAY_HEIGHT] = {0};
  uint8_t frame5[DISPLAY_WIDTH * DISPLAY_HEIGHT] = {0};
  uint8_t frame6[DISPLAY_WIDTH * DISPLAY_HEIGHT] = {0};
  uint8_t frame7[DISPLAY_WIDTH * DISPLAY_HEIGHT] = {0};
  uint8_t frame8[DISPLAY_WIDTH * DISPLAY_HEIGHT] = {0};
  uint8_t frame9[DISPLAY_WIDTH * DISPLAY_HEIGHT] = {0};
  uint8_t frame10[DISPLAY_WIDTH * DISPLAY_HEIGHT] = {0};

  const uint8_t* frame_collection[HATCH_STATUS_FRAME_COUNT +
                                  2 * HATCH_WARNING_REPEAT_SHINE_COUNT] = {
      frame1, frame2, frame3, frame4, frame5,
      frame6, frame7, frame8, frame9, frame10};

  get_hatch_status_frame(390, frame1);
  get_hatch_status_frame(290, frame2);
  get_hatch_status_frame(190, frame3);
  get_hatch_status_frame(90, frame4);
  get_hatch_born_warning_frame(0, frame5);
  get_hatch_born_warning_frame(1, frame6);
  get_hatch_born_warning_frame(0, frame7);
  get_hatch_born_warning_frame(1, frame8);
  get_hatch_born_warning_frame(0, frame9);
  get_hatch_born_warning_frame(1, frame10);

  // show animation
  for (int i = 0; i < repeat_count; ++i) {
    show_anime_with_delay(
        frame_collection,
        HATCH_STATUS_FRAME_COUNT + 2 * HATCH_WARNING_REPEAT_SHINE_COUNT,
        SLEEP_US);
  }
}

/**
 * @brief The example of number test
 *
 * This function will show diffent digits examples of number icon, like
 * 1, 23, 456, 789, 100.
 *
 * Note: 23 can't fill like 023, or it will be recognized as octal format
 * number.
 *
 * @param repeat_count How many times should frame_collection repeat
 */
void num_test(int repeat_count) {
  const int frame_count = 5;
  const component_info num_area_component_info = {
      .x_len = 8,
      .y_len = 8,
      .x_offset = 0,
      .y_offset = 0,
  };
  const base_info screen_info = {
      .width = 16,
      .height = 8,
  };

  // create screens
  uint8_t num_component1[num_area_component_info.x_len *
                         num_area_component_info.y_len];
  memset(num_component1, 0,
         num_area_component_info.x_len * num_area_component_info.y_len);
  uint8_t num_component2[num_area_component_info.x_len *
                         num_area_component_info.y_len];
  memset(num_component2, 0,
         num_area_component_info.x_len * num_area_component_info.y_len);
  uint8_t num_component3[num_area_component_info.x_len *
                         num_area_component_info.y_len];
  memset(num_component3, 0,
         num_area_component_info.x_len * num_area_component_info.y_len);
  uint8_t num_component4[num_area_component_info.x_len *
                         num_area_component_info.y_len];
  memset(num_component4, 0,
         num_area_component_info.x_len * num_area_component_info.y_len);
  uint8_t num_component5[num_area_component_info.x_len *
                         num_area_component_info.y_len];
  memset(num_component5, 0,
         num_area_component_info.x_len * num_area_component_info.y_len);
  get_number_component(1, num_component1);
  get_number_component(23, num_component2);
  get_number_component(456, num_component3);
  get_number_component(789, num_component4);
  get_number_component(100, num_component5);

  uint8_t frame1[screen_info.width * screen_info.height];
  memset(frame1, 0, screen_info.width * screen_info.height);
  uint8_t frame2[screen_info.width * screen_info.height];
  memset(frame2, 0, screen_info.width * screen_info.height);
  uint8_t frame3[screen_info.width * screen_info.height];
  memset(frame3, 0, screen_info.width * screen_info.height);
  uint8_t frame4[screen_info.width * screen_info.height];
  memset(frame4, 0, screen_info.width * screen_info.height);
  uint8_t frame5[screen_info.width * screen_info.height];
  memset(frame5, 0, screen_info.width * screen_info.height);

  uint8_t* num_component_all[frame_count] = {num_component1, num_component2,
                                             num_component3, num_component4,
                                             num_component5};
  stack_component(num_component1, frame1, num_area_component_info, screen_info);
  stack_component(num_component2, frame2, num_area_component_info, screen_info);
  stack_component(num_component3, frame3, num_area_component_info, screen_info);
  stack_component(num_component4, frame4, num_area_component_info, screen_info);
  stack_component(num_component5, frame5, num_area_component_info, screen_info);

  const uint8_t* frame_all[frame_count] = {frame1, frame2, frame3, frame4,
                                           frame5};

  // show animation
  for (int i = 0; i < repeat_count; ++i) {
    show_anime_with_delay(frame_all, frame_count, SLEEP_US);
  }
}

/**
 * @brief The example of cat_idle
 *
 * @param repeat_count How many times should frame_collection repeat
 */
void cat_idle_with_status(int repeat_count) {
  uint8_t cat_idle1[DISPLAY_WIDTH * DISPLAY_HEIGHT] = {0};
  uint8_t cat_idle2[DISPLAY_WIDTH * DISPLAY_HEIGHT] = {0};
  get_cat_idle_frame_with_status_overview(
      FRAME_1, 3, 4, cat_idle1);  // dog idle frame with status overview
  get_cat_idle_frame_with_status_overview(
      FRAME_2, 3, 4, cat_idle2);  // dog idle frame with status overview

  const uint8_t* cat_idle_frame_all[CAT_IDLE_FRAME_COUNT] = {cat_idle1,
                                                             cat_idle2};

  for (int i = 0; i < repeat_count; ++i) {
    show_anime_with_delay(cat_idle_frame_all, CAT_IDLE_FRAME_COUNT, SLEEP_US);
  }
}

/**
 * @brief The example of dog_idle
 *
 * @param repeat_count How many times should frame_collection repeat
 */
void dog_idle_with_status(int repeat_count) {
  uint8_t dog_idle1[DISPLAY_WIDTH * DISPLAY_HEIGHT] = {0};
  uint8_t dog_idle2[DISPLAY_WIDTH * DISPLAY_HEIGHT] = {0};

  get_dog_idle_frame_with_status_overview(
      FRAME_1, 3, 4, dog_idle1);  // dog idle frame with status overview
  get_dog_idle_frame_with_status_overview(
      FRAME_2, 3, 4, dog_idle2);  // dog idle frame with status overview

  const uint8_t* dog_idle_frame_all[DOG_IDLE_FRAME_COUNT] = {dog_idle1,
                                                             dog_idle2};

  for (int i = 0; i < repeat_count; ++i) {
    show_anime_with_delay(dog_idle_frame_all, DOG_IDLE_FRAME_COUNT, SLEEP_US);
  }
}

/**
 * @brief The example of cat_idle with weak status
 *
 * Same as cat_idle_with_status, only passing value different.
 * The case here is hungry trigger weak status.
 *
 * @param repeat_count How many times should frame_collection repeat
 */
void cat_weak_idle_with_status(int repeat_count) {
  uint8_t cat_idle1[DISPLAY_WIDTH * DISPLAY_HEIGHT] = {0};
  uint8_t cat_idle2[DISPLAY_WIDTH * DISPLAY_HEIGHT] = {0};
  // cat idle frame with status overview
  get_cat_idle_frame_with_status_overview(
      FRAME_1, 3, 0, cat_idle1);  // dog idle frame with status overview
  get_cat_idle_frame_with_status_overview(
      FRAME_2, 3, 0, cat_idle2);  // dog idle frame with status overview

  const uint8_t* cat_idle_frame_all[CAT_IDLE_FRAME_COUNT] = {cat_idle1,
                                                             cat_idle2};

  for (int i = 0; i < repeat_count; ++i) {
    show_anime_with_delay(cat_idle_frame_all, CAT_IDLE_FRAME_COUNT, SLEEP_US);
  }
}

/**
 * @brief The example of dog_idle with weak status
 *
 * Same as dog_idle_with_status, only passing value different.
 * The case here is heart poor trigger weak status.
 *
 * @param repeat_count How many times should frame_collection repeat
 */

void dog_weak_idle_with_status(int repeat_count) {
  uint8_t dog_idle1[DISPLAY_WIDTH * DISPLAY_HEIGHT] = {0};
  uint8_t dog_idle2[DISPLAY_WIDTH * DISPLAY_HEIGHT] = {0};
  get_dog_idle_frame_with_status_overview(
      FRAME_1, 0, 4, dog_idle1);  // dog idle frame with status overview
  get_dog_idle_frame_with_status_overview(
      FRAME_2, 0, 4, dog_idle2);  // dog idle frame with status overview

  const uint8_t* dog_idle_frame_all[DOG_IDLE_FRAME_COUNT] = {dog_idle1,
                                                             dog_idle2};

  for (int i = 0; i < repeat_count; ++i) {
    show_anime_with_delay(dog_idle_frame_all, DOG_IDLE_FRAME_COUNT, SLEEP_US);
  }
}

void dog_status_change(int repeat_count) {
  uint8_t dog_status1[DISPLAY_WIDTH * DISPLAY_HEIGHT] = {0};
  uint8_t dog_status2[DISPLAY_WIDTH * DISPLAY_HEIGHT] = {0};
  uint8_t dog_status3[DISPLAY_WIDTH * DISPLAY_HEIGHT] = {0};

  // dog idle frame with status overview
  get_dog_idle_frame_with_status_overview(
      FRAME_1, 3, 4, dog_status1);  // dog idle frame with status overview
  get_dog_idle_frame_with_status_overview(
      FRAME_2, 2, 2, dog_status2);  // dog idle frame with status overview
  get_dog_idle_frame_with_status_overview(
      FRAME_1, 1, 0, dog_status3);  // dog idle frame with status overview

  const uint8_t* dog_idle_frame_all[3] = {dog_status1, dog_status2,
                                          dog_status3};

  for (int i = 0; i < repeat_count; ++i) {
    show_anime_with_delay(dog_idle_frame_all, 3, SLEEP_US);
  }
}

/**
 * @brief The example of pet healing
 *
 * This function will show the pet healing animation.
 *
 * @param repeat_count How many times should frame_collection repeat
 */
void pet_healing(int pet_type, int repeat_count) {
  const uint8_t frame_count = 2;
  uint8_t pet_healing1[DISPLAY_WIDTH * DISPLAY_HEIGHT] = {0};
  uint8_t pet_healing2[DISPLAY_WIDTH * DISPLAY_HEIGHT] = {0};
  get_pet_healing_frame(pet_type, FRAME_1, pet_healing1);
  get_pet_healing_frame(pet_type, FRAME_2, pet_healing2);

  // heart float up > empty
  const uint8_t* pet_healing_frame_all[frame_count] = {
      pet_healing1,
      pet_healing2,
  };

  for (int i = 0; i < repeat_count; ++i) {
    show_anime_with_delay(pet_healing_frame_all, frame_count, SLEEP_US);
  }
}

/**
 * @brief The example of training_selection
 *
 * @param repeat_count How many times should frame_collection repeat
 */
void training_selection(int repeat_count) {
  const uint8_t frame_count = 2;
  uint8_t frame_left[DISPLAY_WIDTH * DISPLAY_HEIGHT] = {0};
  uint8_t frame_right[DISPLAY_WIDTH * DISPLAY_HEIGHT] = {0};
  get_activity_selection_frame(TRAINING, LEFT, frame_left);
  get_activity_selection_frame(TRAINING, RIGHT, frame_right);

  const uint8_t* frame_all[frame_count] = {
      frame_left,
      frame_right,
  };

  for (int i = 0; i < repeat_count; ++i) {
    show_anime_with_delay(frame_all, frame_count, SLEEP_US);
  }
}
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
